develtechmon/ESP32_S3_Bicopter_Flight_Controller/Images/V2_Bicopter/4.jpeg

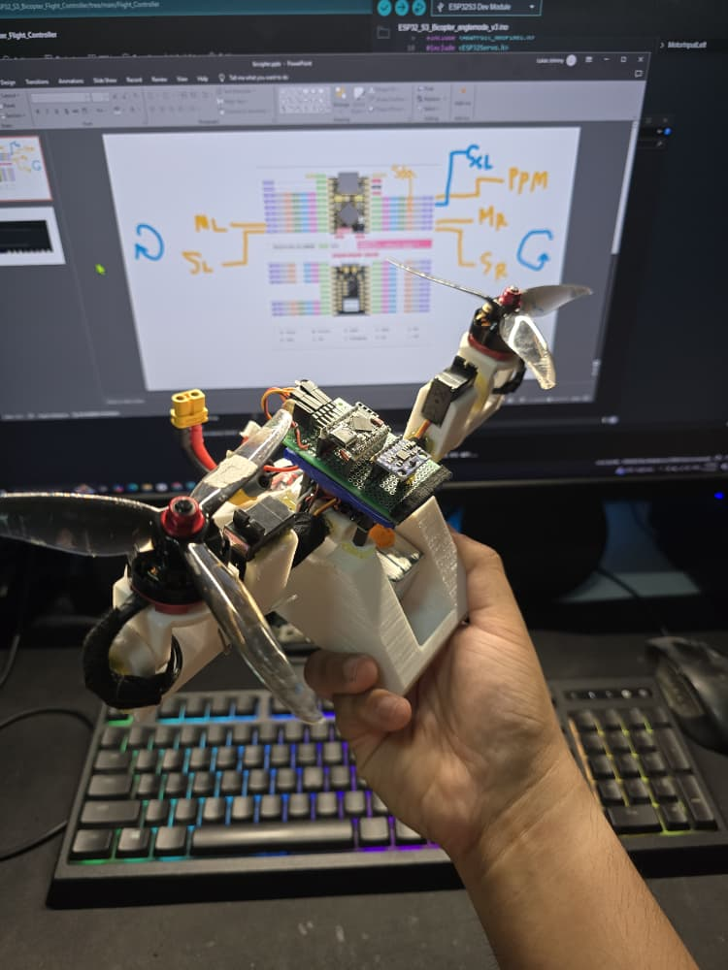
Images/V2_Bicopter/4.jpeg
